harp-tech/device.analoginput/Firmware/AnalogInput/app_funcs.c

#include "app_funcs.h"
#include "app_ios_and_regs.h"
#include "hwbp_core.h"

extern uint16_t pulse_counter_ms;

/************************************************************************/
/* Create pointers to functions                                         */
/************************************************************************/
extern AppRegs app_regs;

void (*app_func_rd_pointer[])(void) = {
	&app_read_REG_START,
	&app_read_REG_ANALOG_INPUTS,
	&app_read_REG_DI0,
	&app_read_REG_RESERVED0,
	&app_read_REG_RESERVED00,
	&app_read_REG_RANGE_AND_INPUT_FILTER,
	&app_read_REG_SAMPLE_FREQUENCY,
	&app_read_REG_DI0_CONF,
	&app_read_REG_DO0_CONF,
	&app_read_REG_DO0_PULSE,
	&app_read_REG_DO_SET,
	&app_read_REG_DO_CLEAR,
	&app_read_REG_DO_TOGGLE,
	&app_read_REG_DO_WRITE,
	&app_read_REG_RESERVED1,
	&app_read_REG_RESERVED2,
	&app_read_REG_TRIGGER_DESTINY,
	&app_read_REG_RESERVED3,
	&app_read_REG_RESERVED4,
	&app_read_REG_RESERVED5,
	&app_read_REG_RESERVED6,
	&app_read_REG_RESERVED7,
	&app_read_REG_RESERVED8,
	&app_read_REG_RESERVED9,
	&app_read_REG_RESERVED10,
	&app_read_REG_RESERVED11,
	&app_read_REG_DO0_CH,
	&app_read_REG_DO1_CH,
	&app_read_REG_DO2_CH,
	&app_read_REG_DO3_CH,
	&app_read_REG_RESERVED12,
	&app_read_REG_RESERVED13,
	&app_read_REG_RESERVED14,
	&app_read_REG_RESERVED15,
	&app_read_REG_DO0_TH_VALUE,
	&app_read_REG_DO1_TH_VALUE,
	&app_read_REG_DO2_TH_VALUE,
	&app_read_REG_DO3_TH_VALUE,
	&app_read_REG_RESERVED17,
	&app_read_REG_RESERVED18,
	&app_read_REG_RESERVED19,
	&app_read_REG_RESERVED20,
	&app_read_REG_DO0_TH_UP_SAMPLES,
	&app_read_REG_DO1_TH_UP_SAMPLES,
	&app_read_REG_DO2_TH_UP_SAMPLES,
	&app_read_REG_DO3_TH_UP_SAMPLES,
	&app_read_REG_RESERVED21,
	&app_read_REG_RESERVED22,
	&app_read_REG_RESERVED23,
	&app_read_REG_RESERVED24,
	&app_read_REG_DO0_TH_DOWN_SAMPLES,
	&app_read_REG_DO1_TH_DOWN_SAMPLES,
	&app_read_REG_DO2_TH_DOWN_SAMPLES,
	&app_read_REG_DO3_TH_DOWN_SAMPLES,
	&app_read_REG_RESERVED25,
	&app_read_REG_RESERVED26,
	&app_read_REG_RESERVED27,
	&app_read_REG_RESERVED28,
	&app_read_REG_RESERVED29
};

bool (*app_func_wr_pointer[])(void*) = {
	&app_write_REG_START,
	&app_write_REG_ANALOG_INPUTS,
	&app_write_REG_DI0,
	&app_write_REG_RESERVED0,
	&app_write_REG_RESERVED00,
	&app_write_REG_RANGE_AND_INPUT_FILTER,
	&app_write_REG_SAMPLE_FREQUENCY,
	&app_write_REG_DI0_CONF,
	&app_write_REG_DO0_CONF,
	&app_write_REG_DO0_PULSE,
	&app_write_REG_DO_SET,
	&app_write_REG_DO_CLEAR,
	&app_write_REG_DO_TOGGLE,
	&app_write_REG_DO_WRITE,
	&app_write_REG_RESERVED1,
	&app_write_REG_RESERVED2,
	&app_write_REG_TRIGGER_DESTINY,
	&app_write_REG_RESERVED3,
	&app_write_REG_RESERVED4,
	&app_write_REG_RESERVED5,
	&app_write_REG_RESERVED6,
	&app_write_REG_RESERVED7,
	&app_write_REG_RESERVED8,
	&app_write_REG_RESERVED9,
	&app_write_REG_RESERVED10,
	&app_write_REG_RESERVED11,
	&app_write_REG_DO0_CH,
	&app_write_REG_DO1_CH,
	&app_write_REG_DO2_CH,
	&app_write_REG_DO3_CH,
	&app_write_REG_RESERVED12,
	&app_write_REG_RESERVED13,
	&app_write_REG_RESERVED14,
	&app_write_REG_RESERVED15,
	&app_write_REG_DO0_TH_VALUE,
	&app_write_REG_DO1_TH_VALUE,
	&app_write_REG_DO2_TH_VALUE,
	&app_write_REG_DO3_TH_VALUE,
	&app_write_REG_RESERVED17,
	&app_write_REG_RESERVED18,
	&app_write_REG_RESERVED19,
	&app_write_REG_RESERVED20,
	&app_write_REG_DO0_TH_UP_SAMPLES,
	&app_write_REG_DO1_TH_UP_SAMPLES,
	&app_write_REG_DO2_TH_UP_SAMPLES,
	&app_write_REG_DO3_TH_UP_SAMPLES,
	&app_write_REG_RESERVED21,
	&app_write_REG_RESERVED22,
	&app_write_REG_RESERVED23,
	&app_write_REG_RESERVED24,
	&app_write_REG_DO0_TH_DOWN_SAMPLES,
	&app_write_REG_DO1_TH_DOWN_SAMPLES,
	&app_write_REG_DO2_TH_DOWN_SAMPLES,
	&app_write_REG_DO3_TH_DOWN_SAMPLES,
	&app_write_REG_RESERVED25,
	&app_write_REG_RESERVED26,
	&app_write_REG_RESERVED27,
	&app_write_REG_RESERVED28,
	&app_write_REG_RESERVED29
};


/************************************************************************/
/* REG_START                                                            */
/************************************************************************/
void app_read_REG_START(void)
{
	//app_regs.REG_START = 0;

}

bool app_write_REG_START(void *a)
{
	uint8_t reg = *((uint8_t*)a);

	app_regs.REG_START = reg;
	return true;
}


/************************************************************************/
/* REG_ANALOG_INPUTS                                                    */
/************************************************************************/
// This register is an array with 4 positions
void app_read_REG_ANALOG_INPUTS(void)
{
	//app_regs.REG_ANALOG_INPUTS[0] = 0;

}

bool app_write_REG_ANALOG_INPUTS(void *a)
{
	int16_t *reg = ((int16_t*)a);

	app_regs.REG_ANALOG_INPUTS[0] = reg[0];
	return true;
}


/************************************************************************/
/* REG_DI0                                                              */
/************************************************************************/
void app_read_REG_DI0(void)
{
	if (read_DI0)
		app_regs.REG_DI0 = B_DI0;
	else
		app_regs.REG_DI0 = 0;
}

bool app_write_REG_DI0(void *a)
{
	uint8_t reg = *((uint8_t*)a);

	app_regs.REG_DI0 = reg;
	return true;
}


/************************************************************************/
/* REG_RESERVED0                                                        */
/************************************************************************/
void app_read_REG_RESERVED0(void)
{
	//app_regs.REG_RESERVED0 = 0;

}

bool app_write_REG_RESERVED0(void *a)
{
	uint8_t reg = *((uint8_t*)a);

	app_regs.REG_RESERVED0 = reg;
	return true;
}


/************************************************************************/
/* REG_RESERVED00                                                       */
/************************************************************************/
void app_read_REG_RESERVED00(void)
{
	//app_regs.REG_RESERVED00 = 0;

}

bool app_write_REG_RESERVED00(void *a)
{
	uint8_t reg = *((uint8_t*)a);

	app_regs.REG_RESERVED00 = reg;
	return true;
}


/************************************************************************/
/* REG_RANGE_AND_INPUT_FILTER                                           */
/************************************************************************/
void app_read_REG_RANGE_AND_INPUT_FILTER(void) {}
bool app_write_REG_RANGE_AND_INPUT_FILTER(void *a)
{
	uint8_t reg = *((uint8_t*)a);
	
	if (reg & ~MSK_RANGE_AND_INPUT_FILTER)
		return false;
	
	PORTD.OUTCLR = 0x1C;
	PORTD.OUTSET = (reg << 2) & 0x1C;
	
	
	if (reg & 0x10)
		set_RANGE;
	else
		clr_RANGE;

	app_regs.REG_RANGE_AND_INPUT_FILTER = reg;
	return true;
}


/************************************************************************/
/* REG_SAMPLE_FREQUENCY                                                 */
/************************************************************************/
void app_read_REG_SAMPLE_FREQUENCY(void) {}
bool app_write_REG_SAMPLE_FREQUENCY(void *a)
{
	uint8_t reg = *((uint8_t*)a);
	
	if (reg & ~MSK_SAMPLE_FREQUENCY)
		return false;

	app_regs.REG_SAMPLE_FREQUENCY = reg;
	return true;
}


/************************************************************************/
/* REG_DI0_CONF                                                         */
/************************************************************************/
void app_read_REG_DI0_CONF(void) {}
bool app_write_REG_DI0_CONF(void *a)
{
	uint8_t reg = *((uint8_t*)a);
	
	if (reg & (~MSK_DI0_SEL))
		return false;

	app_regs.REG_DI0_CONF = reg;
	return true;
}


/************************************************************************/
/* REG_DO0_CONF                                                         */
/************************************************************************/
void app_read_REG_DO0_CONF(void)
{
	//app_regs.REG_DO0_CONF = 0;

}

bool app_write_REG_DO0_CONF(void *a)
{
	uint8_t reg = *((uint8_t*)a);

	app_regs.REG_DO0_CONF = reg;
	return true;
}


/************************************************************************/
/* REG_DO0_PULSE                                                        */
/************************************************************************/
void app_read_REG_DO0_PULSE(void)
{
	//app_regs.REG_DO0_PULSE = 0;

}

bool app_write_REG_DO0_PULSE(void *a)
{
	uint8_t reg = *((uint8_t*)a);
	
	if (reg < 1)
		return false;
		
	if (reg > 250)
		return false;

	app_regs.REG_DO0_PULSE = reg;
	return true;
}


/************************************************************************/
/* REG_DO_SET                                                           */
/************************************************************************/
void app_read_REG_DO_SET(void) {}
bool app_write_REG_DO_SET(void *a)
{
	uint8_t reg = *((uint8_t*)a);
	
	if ((reg & B_DO0) && (app_regs.REG_TRIGGER_DESTINY != GM_TRIG_TO_DO0))
	{
		if (app_regs.REG_DO0_CONF == GM_DO0_DIG)
		{
			set_DO0;
		}
		if (app_regs.REG_DO0_CONF == GM_DO0_PULSE)
		{
			set_DO0;
			pulse_counter_ms = app_regs.REG_DO0_PULSE + 1;
		}
	}
	
	if ((reg & B_DO1) && (app_regs.REG_TRIGGER_DESTINY != GM_TRIG_TO_DO1)) set_DO1;
	if ((reg & B_DO2) && (app_regs.REG_TRIGGER_DESTINY != GM_TRIG_TO_DO2)) set_DO2;
	if ((reg & B_DO3) && (app_regs.REG_TRIGGER_DESTINY != GM_TRIG_TO_DO3)) set_DO3;
	
	app_regs.REG_DO_SET = reg;
	return true;
}


/************************************************************************/
/* REG_DO_CLEAR                                                         */
/************************************************************************/
void app_read_REG_DO_CLEAR(void) {}
bool app_write_REG_DO_CLEAR(void *a)
{
	uint8_t reg = *((uint8_t*)a);
	
	if ((reg & B_DO0) && (app_regs.REG_TRIGGER_DESTINY != GM_TRIG_TO_DO0))
	{
		if (app_regs.REG_DO0_CONF != GM_DO0_TGL_EACH_SEC)
		{
			clr_DO0;
			pulse_counter_ms = 0;
		}
	}
	
	if ((reg & B_DO1) && (app_regs.REG_TRIGGER_DESTINY != GM_TRIG_TO_DO1)) clr_DO1;
	if ((reg & B_DO2) && (app_regs.REG_TRIGGER_DESTINY != GM_TRIG_TO_DO2)) clr_DO2;
	if ((reg & B_DO3) && (app_regs.REG_TRIGGER_DESTINY != GM_TRIG_TO_DO3)) clr_DO3;
	
	app_regs.REG_DO_CLEAR = reg;
	return true;
}


/************************************************************************/
/* REG_DO_TOGGLE                                                        */
/************************************************************************/
void app_read_REG_DO_TOGGLE(void) {}
bool app_write_REG_DO_TOGGLE(void *a)
{
	uint8_t reg = *((uint8_t*)a);
	
	if ((reg & B_DO0) && (app_regs.REG_TRIGGER_DESTINY != GM_TRIG_TO_DO0))
	{
		if (read_DO0)
		{
			if (app_regs.REG_DO0_CONF != GM_DO0_TGL_EACH_SEC)
			{
				clr_DO0;
				pulse_counter_ms = 0;
			}
		}
		else
		{
			if (app_regs.REG_DO0_CONF == GM_DO0_DIG)
			{
				set_DO0;
			}
			if (app_regs.REG_DO0_CONF == GM_DO0_PULSE)
			{
				set_DO0;
				pulse_counter_ms = app_regs.REG_DO0_PULSE + 1;
			}
		}
	}
	
	if ((reg & B_DO1) && (app_regs.REG_TRIGGER_DESTINY != GM_TRIG_TO_DO1)) tgl_DO1;
	if ((reg & B_DO2) && (app_regs.REG_TRIGGER_DESTINY != GM_TRIG_TO_DO2)) tgl_DO2;
	if ((reg & B_DO3) && (app_regs.REG_TRIGGER_DESTINY != GM_TRIG_TO_DO3)) tgl_DO3;
	
	app_regs.REG_DO_TOGGLE = reg;
	return true;
}


/************************************************************************/
/* REG_DO_WRITE                                                         */
/************************************************************************/
void app_read_REG_DO_WRITE(void)
{
	app_regs.REG_DO_WRITE = PORTA_IN & 0x0F;
}
bool app_write_REG_DO_WRITE(void *a)
{
	uint8_t reg = *((uint8_t*)a);
	
	if ((app_regs.REG_TRIGGER_DESTINY != GM_TRIG_TO_DO0) && (app_regs.REG_DO0_CONF != GM_DO0_TGL_EACH_SEC))
	{
		if (reg & B_DO0)
		{
			set_DO0;
			
			if (app_regs.REG_DO0_CONF == GM_DO0_PULSE)
			{
				pulse_counter_ms = app_regs.REG_DO0_PULSE + 1;
			}
		}
		else
		{
			clr_DO0;
			pulse_counter_ms = 0;
		}
	}
	
	if ((reg & B_DO1) && (app_regs.REG_TRIGGER_DESTINY != GM_TRIG_TO_DO1)) set_DO1; else clr_DO1;
	if ((reg & B_DO2) && (app_regs.REG_TRIGGER_DESTINY != GM_TRIG_TO_DO2)) set_DO2; else clr_DO2;
	if ((reg & B_DO3) && (app_regs.REG_TRIGGER_DESTINY != GM_TRIG_TO_DO3)) set_DO3; else clr_DO3;

	app_regs.REG_DO_WRITE = PORTA_OUT & 0x0F;
	return true;
}


/************************************************************************/
/* REG_RESERVED1                                                        */
/************************************************************************/
void app_read_REG_RESERVED1(void)
{
	//app_regs.REG_RESERVED1 = 0;

}

bool app_write_REG_RESERVED1(void *a)
{
	uint8_t reg = *((uint8_t*)a);

	app_regs.REG_RESERVED1 = reg;
	return true;
}


/************************************************************************/
/* REG_RESERVED2                                                        */
/************************************************************************/
void app_read_REG_RESERVED2(void)
{
	//app_regs.REG_RESERVED2 = 0;

}

bool app_write_REG_RESERVED2(void *a)
{
	uint8_t reg = *((uint8_t*)a);

	app_regs.REG_RESERVED2 = reg;
	return true;
}


/************************************************************************/
/* REG_TRIGGER_DESTINY                                                  */
/************************************************************************/
void app_read_REG_TRIGGER_DESTINY(void) {}
bool app_write_REG_TRIGGER_DESTINY(void *a)
{
	uint8_t reg = *((uint8_t*)a);
	
	if (reg & (~MSK_TRIG_TO_DO0))
		return false;

	app_regs.REG_TRIGGER_DESTINY = reg;
	return true;
}


/************************************************************************/
/* REG_RESERVED3                                                        */
/************************************************************************/
void app_read_REG_RESERVED3(void)
{
	//app_regs.REG_RESERVED3 = 0;

}

bool app_write_REG_RESERVED3(void *a)
{
	int16_t reg = *((int16_t*)a);

	app_regs.REG_RESERVED3 = reg;
	return true;
}


/************************************************************************/
/* REG_RESERVED4                                                        */
/************************************************************************/
void app_read_REG_RESERVED4(void)
{
	//app_regs.REG_RESERVED4 = 0;

}

bool app_write_REG_RESERVED4(void *a)
{
	int16_t reg = *((int16_t*)a);

	app_regs.REG_RESERVED4 = reg;
	return true;
}


/************************************************************************/
/* REG_RESERVED5                                                        */
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
/************************************************************************/
void app_read_REG_RESERVED27(void)
{
	//app_regs.REG_RESERVED27 = 0;

}

bool app_write_REG_RESERVED27(void *a)
{
	uint16_t reg = *((uint16_t*)a);

	app_regs.REG_RESERVED27 = reg;
	return true;
}


/************************************************************************/
/* REG_RESERVED28                                                       */
/************************************************************************/
void app_read_REG_RESERVED28(void)
{
	//app_regs.REG_RESERVED28 = 0;

}

bool app_write_REG_RESERVED28(void *a)
{
	uint16_t reg = *((uint16_t*)a);

	app_regs.REG_RESERVED28 = reg;
	return true;
}


/************************************************************************/
/* REG_RESERVED29                                                       */
/************************************************************************/
void app_read_REG_RESERVED29(void)
{
	//app_regs.REG_RESERVED29 = 0;

}

bool app_write_REG_RESERVED29(void *a)
{
	uint8_t reg = *((uint8_t*)a);

	app_regs.REG_RESERVED29 = reg;
	return true;
}
